greasemonkey-btbm/Tekprobe-USB-power-supply/Drawings - images/61400413321.png

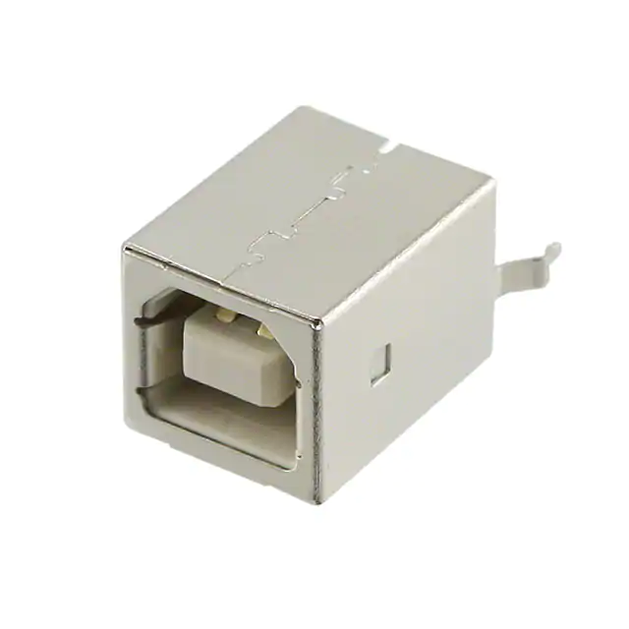
Drawings - images/61400413321.png
