greasemonkey-btbm/Tekprobe-USB-power-supply/Drawings - images/691242510009.png

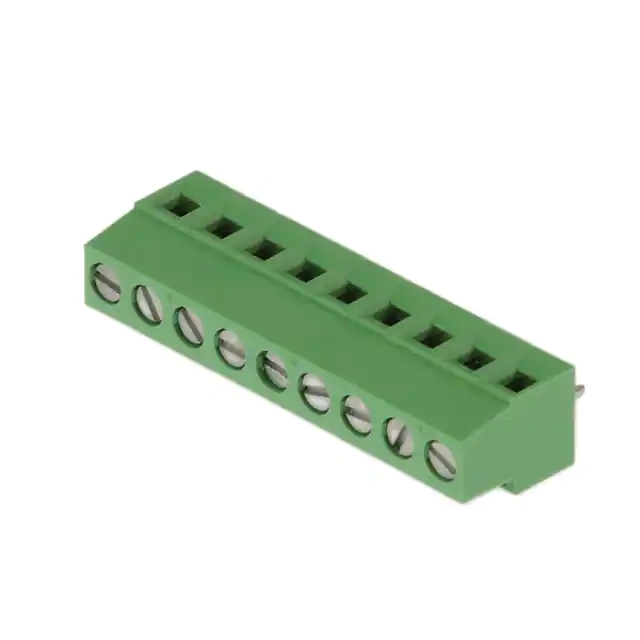
Drawings - images/691242510009.png
